Bobik128/ESP32S3-xiao-phototrap/images/20260511_151443.jpg

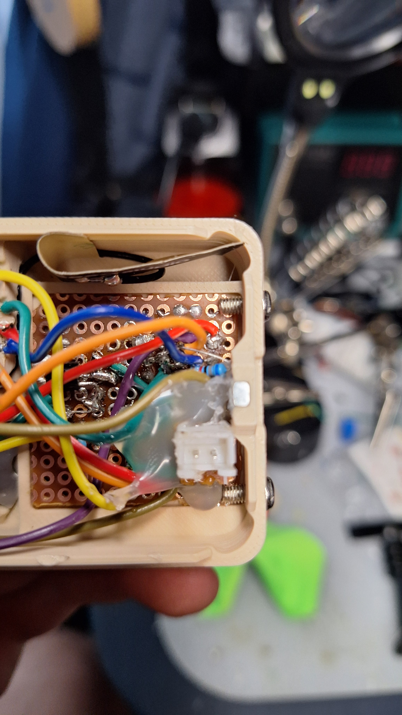
images/20260511_151443.jpg
